Mottramlabs/ESP8266-WiFi-PIR-Sensor/Firmware/MQTT_PIR_MLP201154_V1/MQTT_Settings.h

/*
      MQTT Broker and topic
*/

// MQTT Broker, change as required
const char* mqtt_server = "192.168.1.10";

// MQTT Topics
const char* InStatus = "PIR/Status";
const char* InControl = "PIR/Control";

// the ESP8266's MAC address is normally used to send a message to a selected device. 
// below is the address used to broadcast to all devices subscribed to the above topic.
String Broadcast_All = "*ALL";
